wjk5117/Polaris/Evaluation/Data/Default_Tag/RawData_2.csv

 | Time Stamp | Sensor 1 | Sensor 2 | Sensor 3 | Sensor 4 | Sensor 5 | Sensor 6 | Sensor 7 | Sensor 8 | Sensor 9
0 | 0.0 | (70.65, 30.15, 76.472) | (14.7, -37.8, 32.186) | (41.55, 26.85, 85.91) | (16.2, -4.95, 28.314) | (8.7, -16.2, 40.898) | (1.65, -6.0, 27.346) | (-4.95, -9.75, 40.414) | (9.45, -11.4, 28.314) | (1.35, -21.15, 33.154)
1 | 0.01 | (70.5, 28.8, 75.504) | (14.4, -41.4, 29.524) | (42.45, 22.8, 83.974) | (17.85, -5.1, 28.798) | (9.75, -17.25, 41.866) | (0.0, -7.35, 26.378) | (-4.2, -8.7, 41.624) | (7.35, -12.6, 29.766) | (1.95, -20.85, 33.396)
2 | 0.02 | (70.2, 29.4, 76.23) | (17.4, -37.35, 33.154) | (43.35, 28.35, 82.038) | (18.0, -6.45, 26.862) | (8.4, -15.75, 40.414) | (1.8, -8.25, 26.136) | (-2.55, -9.6, 42.592) | (6.75, -11.1, 31.702) | (0.75, -21.45, 35.574)
3 | 0.03 | (70.8, 30.3, 77.198) | (15.3, -39.15, 32.67) | (43.05, 26.7, 86.394) | (18.3, -5.25, 27.104) | (9.6, -16.2, 44.286) | (-1.05, -6.3, 27.588) | (-3.9, -7.35, 40.172) | (9.3, -13.05, 29.04) | (2.85, -22.2, 35.09)
4 | 0.04 | (70.8, 30.15, 75.262) | (15.6, -37.8, 34.122) | (46.65, 23.85, 83.974) | (18.0, -6.9, 28.072) | (8.1, -16.5, 44.044) | (0.3, -7.95, 27.346) | (-3.9, -8.7, 42.108) | (8.85, -10.35, 29.524) | (1.8, -21.75, 34.122)
5 | 0.05 | (69.9, 28.95, 75.746) | (13.2, -38.1, 31.218) | (40.2, 27.45, 83.248) | (18.15, -7.5, 26.862) | (12.15, -16.5, 42.834) | (-0.75, -6.15, 26.862) | (-3.0, -8.4, 41.382) | (8.7, -11.7, 28.072) | (1.2, -21.45, 32.67)
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
306 | 3.0599999999999787 | (70.35, 27.3, 76.956) | (14.7, -39.9, 33.638) | (37.95, 19.2, 79.86) | (18.45, -10.35, 28.798) | (9.6, -21.3, 41.382) | (2.25, -10.65, 23.716) | (-1.65, -12.3, 39.93) | (9.9, -14.55, 25.894) | (2.55, -23.4, 32.186)
