wjk5117/Polaris/Evaluation/Data/Default_Tag/RawData_3.csv

 | Time Stamp | Sensor 1 | Sensor 2 | Sensor 3 | Sensor 4 | Sensor 5 | Sensor 6 | Sensor 7 | Sensor 8 | Sensor 9
0 | 0.0 | (55.65, 11.4, 42.108) | (31.5, -13.35, 60.016) | (41.25, 25.2, 81.796) | (16.8, -7.2, 28.314) | (11.25, -17.55, 45.012) | (1.2, -5.1, 25.652) | (-2.25, -6.45, 41.382) | (7.05, -10.65, 29.524) | (2.55, -20.4, 34.606)
1 | 0.01 | (56.25, 8.55, 49.61) | (33.45, -15.0, 63.888) | (42.75, 25.05, 85.91) | (17.1, -7.2, 27.588) | (10.8, -15.9, 42.108) | (3.15, -5.85, 27.588) | (-3.45, -10.35, 42.592) | (9.9, -10.2, 30.25) | (2.1, -20.85, 31.944)
2 | 0.02 | (58.65, 10.2, 48.4) | (32.55, -12.45, 64.372) | (40.05, 27.15, 82.038) | (17.7, -7.05, 27.83) | (10.5, -16.8, 42.834) | (0.9, -8.4, 27.104) | (-3.3, -9.0, 42.35) | (7.5, -11.1, 30.008) | (1.5, -20.7, 33.88)
3 | 0.03 | (59.7, 8.55, 45.98) | (34.65, -13.65, 66.066) | (41.25, 23.7, 83.248) | (17.55, -6.0, 27.588) | (10.8, -18.0, 43.076) | (-0.3, -7.05, 27.83) | (-3.15, -8.25, 42.592) | (7.95, -9.6, 28.314) | (1.5, -20.25, 33.154)
4 | 0.04 | (56.7, 11.25, 48.642) | (37.95, -12.45, 67.034) | (41.55, 26.7, 83.732) | (16.8, -6.15, 28.556) | (10.65, -18.15, 41.624) | (2.25, -9.0, 26.136) | (-1.8, -9.45, 40.656) | (10.2, -10.05, 28.314) | (3.0, -20.55, 34.122)
5 | 0.05 | (58.5, 9.3, 48.884) | (31.65, -10.65, 67.76) | (40.35, 26.85, 83.248) | (16.95, -6.75, 27.588) | (10.8, -18.15, 42.592) | (1.95, -6.9, 26.378) | (-3.9, -8.85, 40.898) | (9.45, -10.5, 30.25) | (1.95, -18.9, 32.186)
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
305 | 3.049999999999979 | (57.15, 6.45, 47.432) | (36.9, -16.2, 67.76) | (42.15, 20.7, 84.216) | (17.55, -10.5, 29.766) | (10.8, -21.9, 43.076) | (2.4, -9.6, 25.41) | (-1.95, -13.2, 40.656) | (8.55, -12.3, 28.798) | (3.0, -22.2, 33.638)
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
